daltona/pedalboard/sketch/config.h

#ifndef _CONFIG_H__
#define _CONFIG_H__

#define SERIAL_CLOCK    6
#define SERIAL_DATA_OUT 5
#define LED_LATCH       8  // PIN for latching the LEDs shift register
#define AUX_DISP_LATCH  7  // PIN for latching the AUX display

#endif
